IHot98/arduino-uno-rev-3-altium/Arduino UNO Rev 3/3d/CAPC2012X88N EIA 0805.step

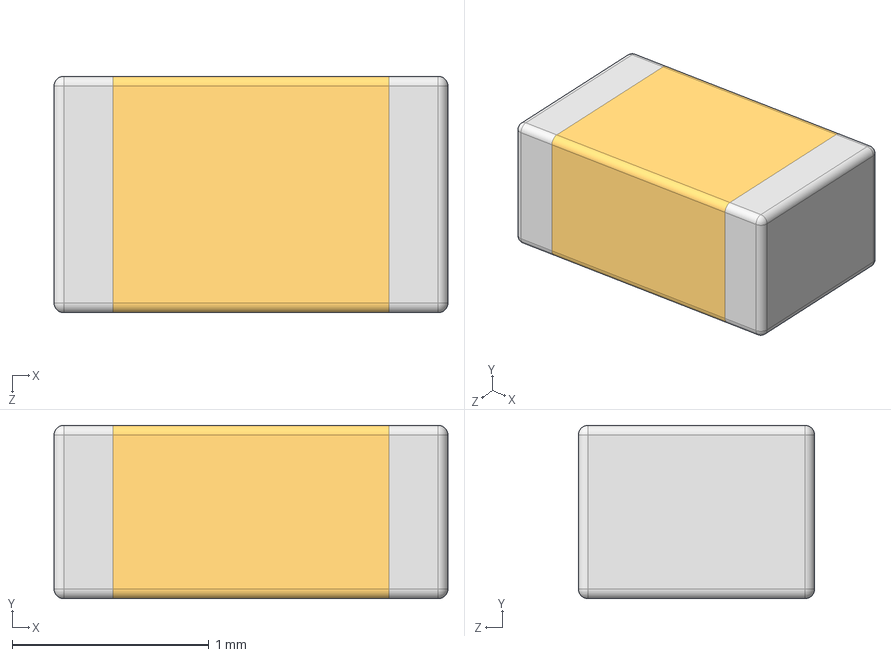
[picture p20: CAD file, 2021-07-22]
Arduino UNO Rev 3/3d/CAPC2012X88N EIA 0805.step
2.00 x 0.88 x 1.20 mm
