IHot98/arduino-uno-rev-3-altium/Arduino UNO Rev 3/3d/m20-7820646_asm.stp

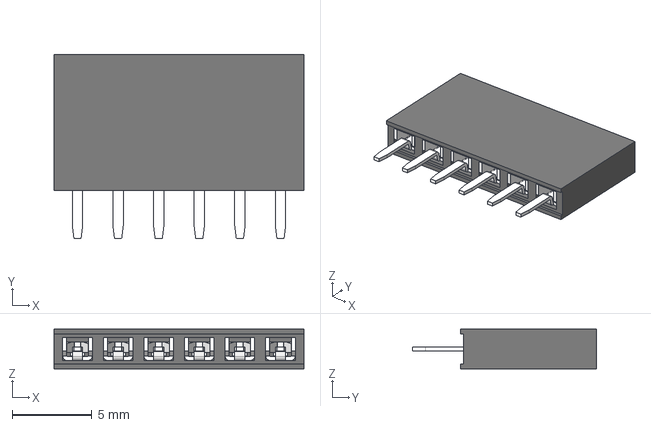
[picture p21: CAD file, 2021-07-22]
Arduino UNO Rev 3/3d/m20-7820646_asm.stp
15.6 x 11.5 x 2.50 mm
M20-78206_MOULD
M20-782_CONTACT x 6
