IHot98/arduino-uno-rev-3-altium/Arduino UNO Rev 3/3d/m20-7821046_asm.stp

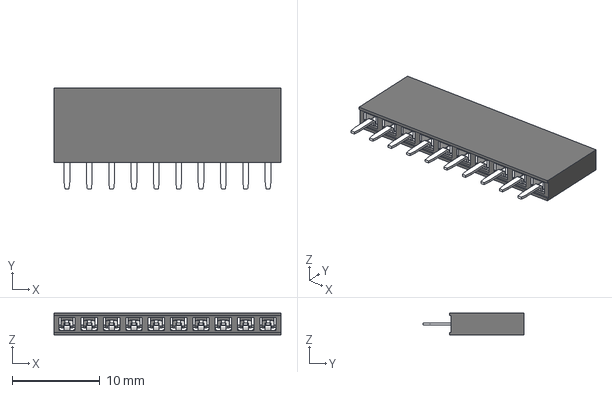
[picture p22: CAD file, 2021-07-22]
Arduino UNO Rev 3/3d/m20-7821046_asm.stp
25.8 x 11.5 x 2.50 mm
M20-78210_MOULD
M20-782_CONTACT x 10
