IHot98/arduino-uno-rev-3-altium/Arduino UNO Rev 3/3d/m20-7820842_asm.stp

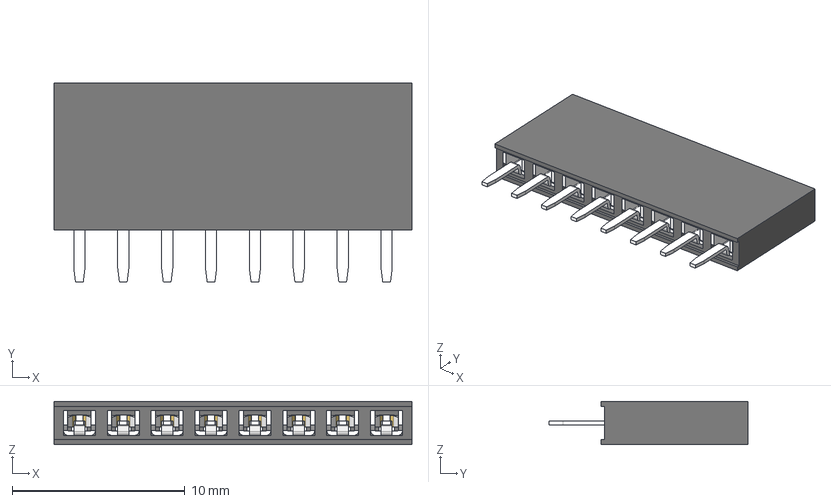
[picture p23: CAD file, 2021-07-22]
Arduino UNO Rev 3/3d/m20-7820842_asm.stp
20.7 x 11.5 x 2.50 mm
M20-78208_MOULD
M20-782_CONTACT x 8
